samin50/DIYKeyboard/imgs/inspo/9b4abea1-d954-40a6-8fb0-e00d4ce0fdc6.jpg

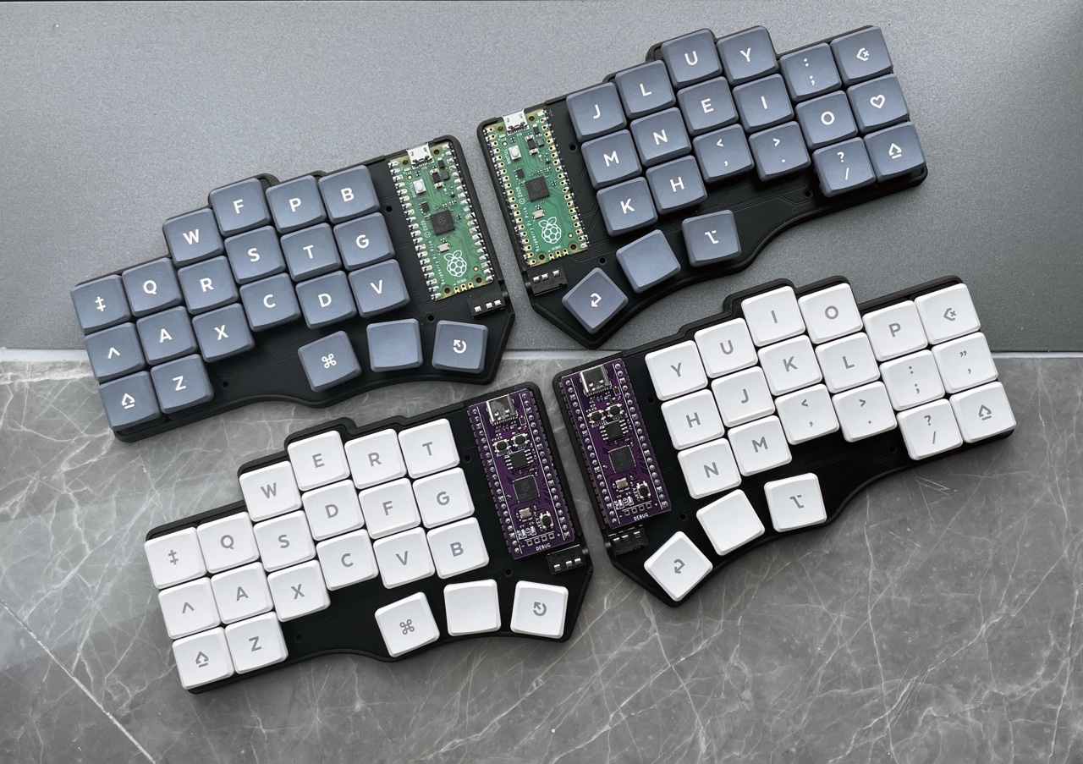
imgs/inspo/9b4abea1-d954-40a6-8fb0-e00d4ce0fdc6.jpg
