samin50/DIYKeyboard/imgs/inspo/1976.jpg

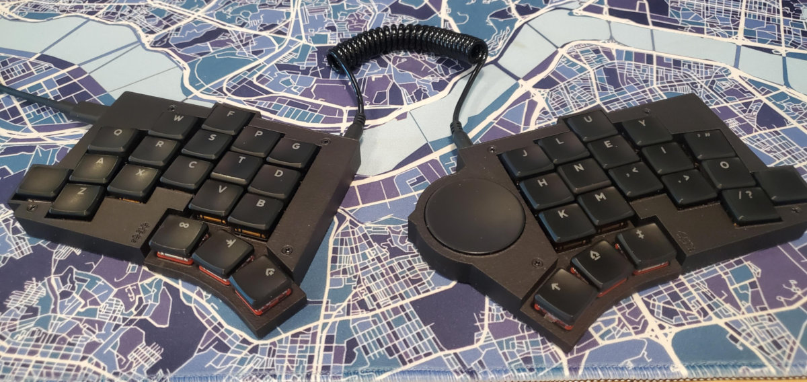
imgs/inspo/1976.jpg
