samin50/DIYKeyboard/imgs/inspo/download (1).jpg

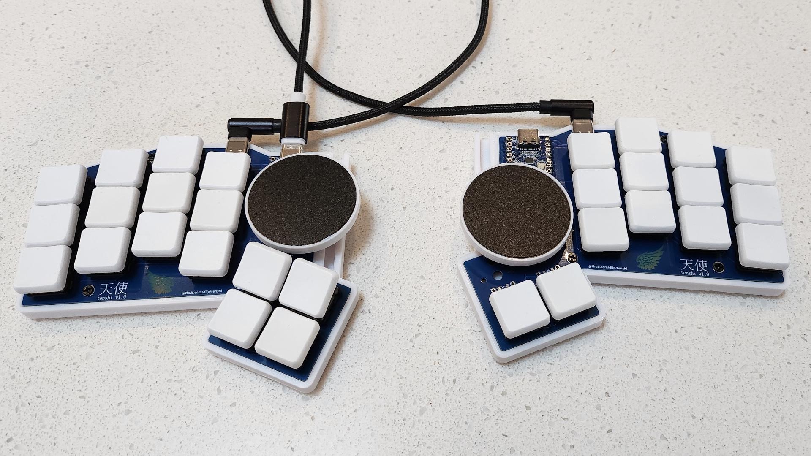
imgs/inspo/download (1).jpg
