samin50/DIYKeyboard/imgs/inspo/download (2).jpg

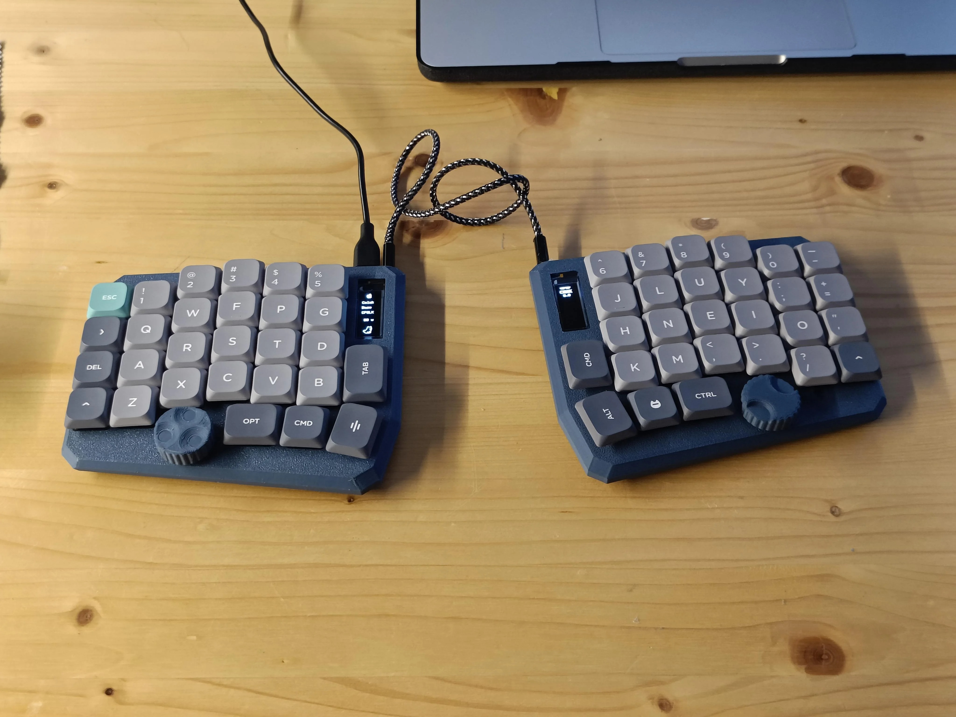
imgs/inspo/download (2).jpg
