samin50/DIYKeyboard/imgs/layers.png

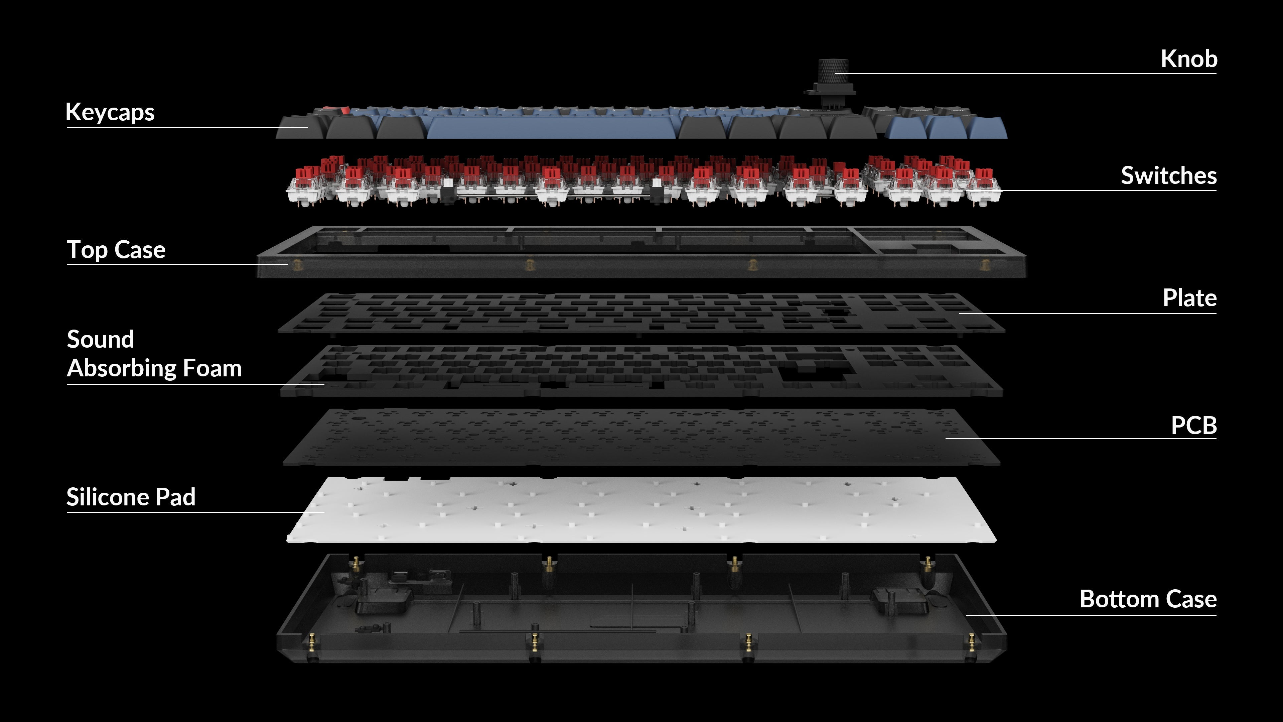
imgs/layers.png
