samin50/DIYKeyboard/imgs/v1.2.png

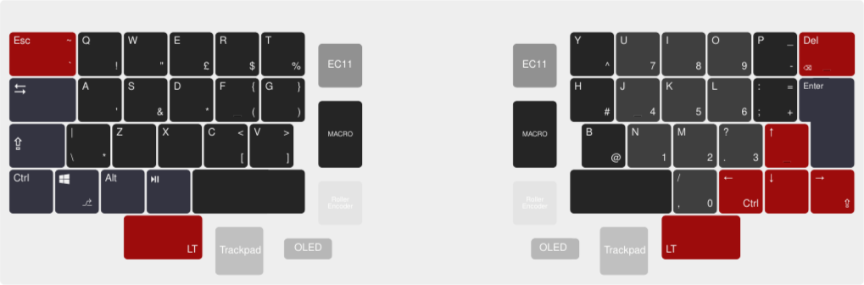
imgs/v1.2.png
